Aluminum-z/Thermos-Bottle/Software/Controller/Core/Inc/main.h

#define TE_SLEEP_Pin GPIO_PIN_13
#define TE_SLEEP_GPIO_Port GPIOC
#define TEMP2_Pin GPIO_PIN_0
#define TEMP2_GPIO_Port GPIOH
#define TEMP1_Pin GPIO_PIN_1
#define TEMP1_GPIO_Port GPIOH
#define LCD_CS_Pin GPIO_PIN_0
#define LCD_CS_GPIO_Port GPIOB
#define LCD_RST_Pin GPIO_PIN_1
#define LCD_RST_GPIO_Port GPIOB
#define LCD_RS_Pin GPIO_PIN_2
#define LCD_RS_GPIO_Port GPIOB
#define FAN_EN_Pin GPIO_PIN_11
#define FAN_EN_GPIO_Port GPIOB
#define KEY_MODE_Pin GPIO_PIN_12
#define KEY_MODE_GPIO_Port GPIOB
#define KEY_ADD_Pin GPIO_PIN_8
#define KEY_ADD_GPIO_Port GPIOA
#define KEY_SUB_Pin GPIO_PIN_9
#define KEY_SUB_GPIO_Port GPIOA
