Aluminum-z/Thermos-Bottle/Software/Controller/User/Drivers/Src/lcdChipFsmc.cpp

/**************************************************************
 * @file    lcdChipFsmc.cpp
 * @brief   Lcd chip libraries for FSMC interface.
 * @author  Alzn
 * @date    2022-09-04
 *************************************************************/
#include "lcdChipFsmc.hpp"

namespace Lcd {

/**
 * @brief   Constructor
 * @author  Alzn
 * @date    2022-03-28
 */
LcdChipNT35510::LcdChipNT35510(const ChipInfoFsmc &deviceInfo) {
  const uint32_t bank1BaseAddress = 0x60000000;
  const uint32_t haddrBaseBitsPos = 26;
  mAddrCom = (uint16_t *)(bank1BaseAddress + (static_cast<size_t>(deviceInfo.chipSelect) << haddrBaseBitsPos));
  mAddrData = mAddrCom;
  mAddrData = (uint16_t *)(reinterpret_cast<size_t>(mAddrData) | 0x01 << (static_cast<size_t>(deviceInfo.regSelect) + 1)); // 16bit数据线的地址需要左移1位
  mResetPin = deviceInfo.resetPin;
}

/**
 * @brief   Initialize chip NT35510.
 * @author  Alzn
 * @date    2022-03-28
 */
void LcdChipNT35510::init(void) {
  if (mResetPin.isValid()) {
    mResetPin.write(Gpio::Reset);
    HAL_Delay(1);
    mResetPin.write(Gpio::Set);
  }
  HAL_Delay(50);
  writeReg(0xF000, 0x55);
  writeReg(0xF001, 0xAA);
  writeReg(0xF002, 0x52);
  writeReg(0xF003, 0x08);
  writeReg(0xF004, 0x01);

  writeReg(0xB600, 0x34);
  writeReg(0xB601, 0x34);
  writeReg(0xB602, 0x34);

  writeReg(0xB000, 0x0D);
  writeReg(0xB001, 0x0D);
  writeReg(0xB002, 0x0D);

  writeReg(0xB700, 0x24);
  writeReg(0xB701, 0x24);
  writeReg(0xB702, 0x24);

  writeReg(0xB100, 0x0D);
  writeReg(0xB101, 0x0D);
  writeReg(0xB102, 0x0D);

  writeReg(0xB800, 0x24);
  writeReg(0xB801, 0x24);
  writeReg(0xB802, 0x24);

  writeReg(0xB200, 0x00);

  writeReg(0xB900, 0x24);
  writeReg(0xB901, 0x24);
  writeReg(0xB902, 0x24);

  writeReg(0xB300, 0x05);
  writeReg(0xB301, 0x05);
  writeReg(0xB302, 0x05);

  writeReg(0xBA00, 0x34);
  writeReg(0xBA01, 0x34);
  writeReg(0xBA02, 0x34);

  writeReg(0xB500, 0x0B);
  writeReg(0xB501, 0x0B);
  writeReg(0xB502, 0x0B);

  writeReg(0xBC00, 0X00);
  writeReg(0xBC01, 0xA3);
  writeReg(0xBC02, 0X00);

  writeReg(0xBD00, 0x00);
  writeReg(0xBD01, 0xA3);
  writeReg(0xBD02, 0x00);

  writeReg(0xBE00, 0x00);
  writeReg(0xBE01, 0x63);

  writeReg(0xD100, 0x00);
  writeReg(0xD101, 0x37);
  writeReg(0xD102, 0x00);
  writeReg(0xD103, 0x52);
  writeReg(0xD104, 0x00);
  writeReg(0xD105, 0x7B);
  writeReg(0xD106, 0x00);
  writeReg(0xD107, 0x99);
  writeReg(0xD108, 0x00);
  writeReg(0xD109, 0xB1);
  writeReg(0xD10A, 0x00);
  writeReg(0xD10B, 0xD2);
  writeReg(0xD10C, 0x00);
  writeReg(0xD10D, 0xF6);
  writeReg(0xD10E, 0x01);
  writeReg(0xD10F, 0x27);
  writeReg(0xD110, 0x01);
  writeReg(0xD111, 0x4E);
  writeReg(0xD112, 0x01);
  writeReg(0xD113, 0x8C);
  writeReg(0xD114, 0x01);
  writeReg(0xD115, 0xBE);
  writeReg(0xD116, 0x02);
  writeReg(0xD117, 0x0B);
  writeReg(0xD118, 0x02);
  writeReg(0xD119, 0x48);
  writeReg(0xD11A, 0x02);
  writeReg(0xD11B, 0x4A);
  writeReg(0xD11C, 0x02);
  writeReg(0xD11D, 0x7E);
  writeReg(0xD11E, 0x02);
  writeReg(0xD11F, 0xBC);
  writeReg(0xD120, 0x02);
  writeReg(0xD121, 0xE1);
  writeReg(0xD122, 0x03);
  writeReg(0xD123, 0x10);
  writeReg(0xD124, 0x03);
  writeReg(0xD125, 0x31);
  writeReg(0xD126, 0x03);
  writeReg(0xD127, 0x5A);
  writeReg(0xD128, 0x03);
  writeReg(0xD129, 0x73);
  writeReg(0xD12A, 0x03);
  writeReg(0xD12B, 0x94);
  writeReg(0xD12C, 0x03);
  writeReg(0xD12D, 0x9F);
  writeReg(0xD12E, 0x03);
  writeReg(0xD12F, 0xB3);
  writeReg(0xD130, 0x03);
  writeReg(0xD131, 0xB9);
  writeReg(0xD132, 0x03);
  writeReg(0xD133, 0xC1);
  writeReg(0xD200, 0x00);
  writeReg(0xD201, 0x37);
  writeReg(0xD202, 0x00);
  writeReg(0xD203, 0x52);
  writeReg(0xD204, 0x00);
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
  writeReg(0xD62E, 0x03);
  writeReg(0xD62F, 0xB3);
  writeReg(0xD630, 0x03);
  writeReg(0xD631, 0xB9);
  writeReg(0xD632, 0x03);
  writeReg(0xD633, 0xC1);

  writeReg(0xF000, 0x55);
  writeReg(0xF001, 0xAA);
  writeReg(0xF002, 0x52);
  writeReg(0xF003, 0x08);
  writeReg(0xF004, 0x00);

  writeReg(0xB000, 0x08);
  writeReg(0xB001, 0x05);
  writeReg(0xB002, 0x02);
  writeReg(0xB003, 0x05);
  writeReg(0xB004, 0x02);
  writeReg(0xB600, 0x08);
  writeReg(0xB500, 0x50);

  writeReg(0xB700, 0x00);
  writeReg(0xB701, 0x00);

  writeReg(0xB800, 0x01);
  writeReg(0xB801, 0x05);
  writeReg(0xB802, 0x05);
  writeReg(0xB803, 0x05);

  writeReg(0xBC00, 0x00);
  writeReg(0xBC01, 0x00);
  writeReg(0xBC02, 0x00);

  writeReg(0xCC00, 0x03);
  writeReg(0xCC01, 0x00);
  writeReg(0xCC02, 0x00);

  writeReg(0xBD00, 0x01);
  writeReg(0xBD01, 0x84);
  writeReg(0xBD02, 0x07);
  writeReg(0xBD03, 0x31);
  writeReg(0xBD04, 0x00);

  writeReg(0xBA00, 0x01);

  writeReg(0xFF00, 0xAA);
  writeReg(0xFF01, 0x55);
  writeReg(0xFF02, 0x25);
  writeReg(0xFF03, 0x01);

  writeReg(0x5500, 0x01);

  writeReg(0x3500, 0x00);
  writeReg(0x3600, 0x60);
  writeReg(0x3a00, 0x55);
  writeCom(0x1100);
  HAL_Delay(120);
  writeCom(0x2900);
  writeCom(0x2C00);
}

/**
 * @brief   Set draw range For NT35510
 * @author  Alzn
 * @date    2022-03-28
 * @param   x1 Left
 * @param   x2 Right
 * @param   y1 Top
 * @param   y2 Buttom
 */
void LcdChipNT35510::setRange(uint16_t x1, uint16_t x2, uint16_t y1, uint16_t y2) {
  writeReg(0X2A00, x1 >> 8);
  writeReg(0X2A01, x1 & 0XFF);
  writeReg(0X2A02, x2 >> 8);
  writeReg(0X2A03, x2 & 0XFF);

  writeReg(0X2B00, y1 >> 8);
  writeReg(0X2B01, y1 & 0XFF);
  writeReg(0X2B02, y2 >> 8);
  writeReg(0X2B03, y2 & 0XFF);

  writeCom(0x2C00);
}

/**
 * @brief   Set the display orientation for NT35510
 * @author  Alzn
 * @date    2022-03-30
 * @param   deviceInfo Change the dispay orientation will update device information.
 * @param   newOrientation The new orientation you want to change to. @ref DispOrientation
 */
void LcdChipNT35510::setOrientation(DispOrientation newOrientation) {
  switch (newOrientation) {
    case DispOrientation::Horizontal:
      writeReg(0x3600, 0x60);
      break;

    case DispOrientation::Vertical:
      writeReg(0x3600, 0x00);
      break;

    case DispOrientation::HoriWithFlip:
      writeReg(0x3600, 0xA0);
      break;

    case DispOrientation::VertWithFlip:
      writeReg(0x3600, 0xC0);
      break;

    default:
      break;
  }
}

/**
 * @brief   Fast write color data.
 * @author  Alzn
 * @date    2022-09-04
 */
void LcdChipNT35510::fillColor(uint16_t color, size_t num) {
  const int32_t divNum = 4;
  while (num >= divNum) {
    writeData(color);
    writeData(color);
    writeData(color);
    writeData(color);
    num -= divNum;
  }
  switch (num) {
    case 3:
      writeData(color);
    case 2:
      writeData(color);
    case 1:
      writeData(color);
    default:
      break;
  }
}
} // namespace Lcd

/* END OF FILE */
