Aluminum-z/Thermos-Bottle/Software/Controller/User/Drivers/Src/lcdFont.cpp

/**************************************************************
 * @file    lcdFont.cpp
 * @brief   Font library.
 * @author  Alzn
 * @date    2022-03-29
 *************************************************************/

#include "lcdFont.hpp"

namespace Lcd {
namespace Font {

/**
 * @brief ASCII Font
 * Font       : Consolas
 * Font Size  : 16
 * Font Style : Normal
 * Width      : 8
 * Height     : 14
 * */
static const uint8_t fontDataConsolas16n8x14[] = {
  //U+0020( )
  0x00,0x00,0x00,0x00,0x00,0x00,0x00,0x00,0x00,0x00,0x00,0x00,0x00,0x00,
  //U+0021(!)
  0x00,0x10,0x10,0x10,0x10,0x10,0x10,0x10,0x00,0x18,0x18,0x00,0x00,0x00,
  //U+0022(")
  0x00,0x6C,0x6C,0x6C,0x00,0x00,0x00,0x00,0x00,0x00,0x00,0x00,0x00,0x00,
  //U+0023(#)
  0x00,0x00,0x24,0x24,0xFE,0x24,0x48,0xFE,0x48,0x48,0x48,0x00,0x00,0x00,
  //U+0024($)
  0x00,0x08,0x3C,0x48,0x50,0x70,0x1C,0x16,0x12,0x12,0x7C,0x10,0x10,0x00,
  //U+0025(%)
  0x00,0x62,0x94,0x9C,0x68,0x10,0x10,0x26,0x69,0x49,0x86,0x00,0x00,0x00,
  //U+0026(&)
  0x00,0x30,0x48,0x48,0x78,0x30,0x74,0x94,0x8C,0x8C,0x76,0x00,0x00,0x00,
  //U+0027(')
  0x00,0x18,0x18,0x18,0x00,0x00,0x00,0x00,0x00,0x00,0x00,0x00,0x00,0x00,
  //U+0028(()
  0x00,0x04,0x08,0x10,0x10,0x20,0x20,0x20,0x20,0x20,0x10,0x10,0x08,0x04,
  //U+0029())
  0x00,0x40,0x20,0x10,0x10,0x08,0x08,0x08,0x08,0x08,0x10,0x10,0x20,0x40,
  //U+002A(*)
  0x00,0x08,0x2A,0x1C,0x1C,0x2A,0x08,0x00,0x00,0x00,0x00,0x00,0x00,0x00,
  //U+002B(+)
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
  .width        = 12,
  .height       = 20,
  .bytePerChar  = 40,
  .byte         = sizeof(fontDataStraightLine12x20),
  .charStart    = 45,
  .charEnd      = 57,
  .pData       = fontDataStraightLine12x20,
};


} // namespace Font
} // namespace Lcd

/* END OF FILE */
