Aluminum-z/Thermos-Bottle/Software/Controller/User/App/Inc/userMain.hpp

/**************************************************************
 * @file    userMain.hpp
 * @brief   
 * @author  Alzn
 * @date    2022-03-28
 **************************************************************/
#ifndef _USERMAIN_H_
#define _USERMAIN_H_

void userMain(void);

#endif /* _USERMAIN_H_ */

/* END OF FILE */
